DangerousPrototypes/BusPirate5-hardware/adapter-ir-toy-3REV3/datasheets/irm-36xxj7.png

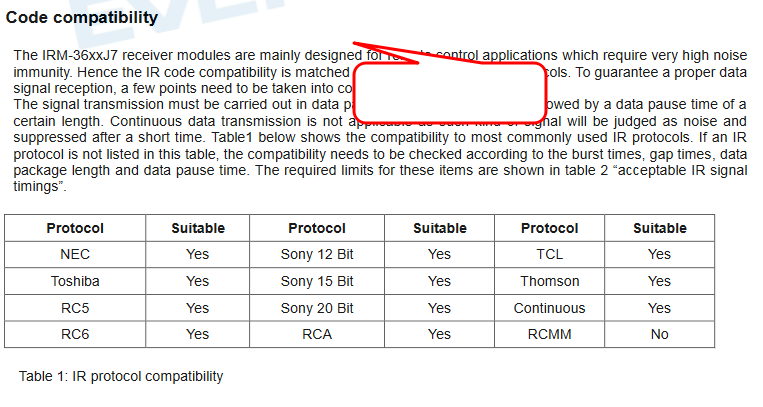
adapter-ir-toy-3REV3/datasheets/irm-36xxj7.png
