DangerousPrototypes/BusPirate5-hardware/bus_pirate_pcb/6-REV2B/6-REV2b.jpg

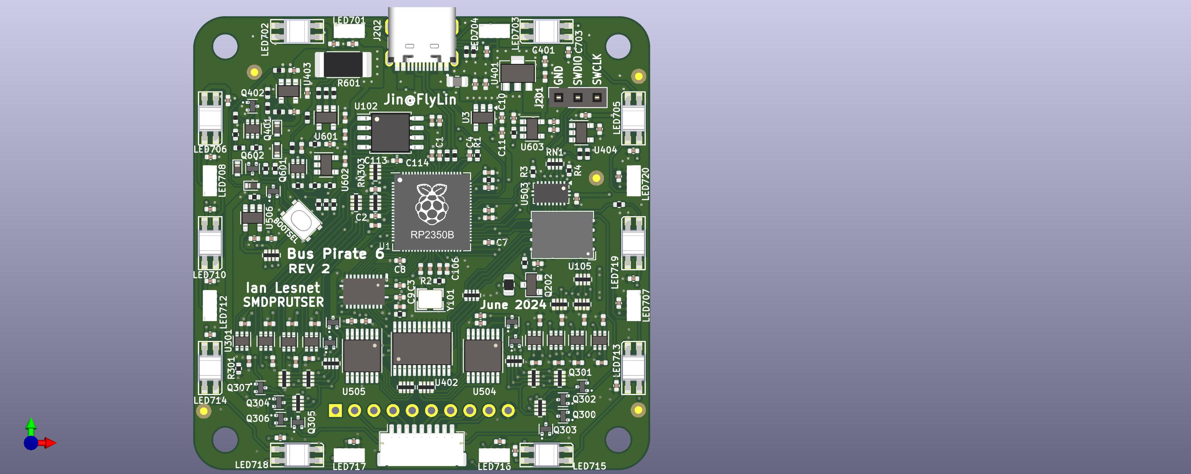
bus_pirate_pcb/6-REV2B/6-REV2b.jpg
