DangerousPrototypes/BusPirate5-hardware/bus_pirate_pcb/6-REV2B/6r2-pcb-top.png

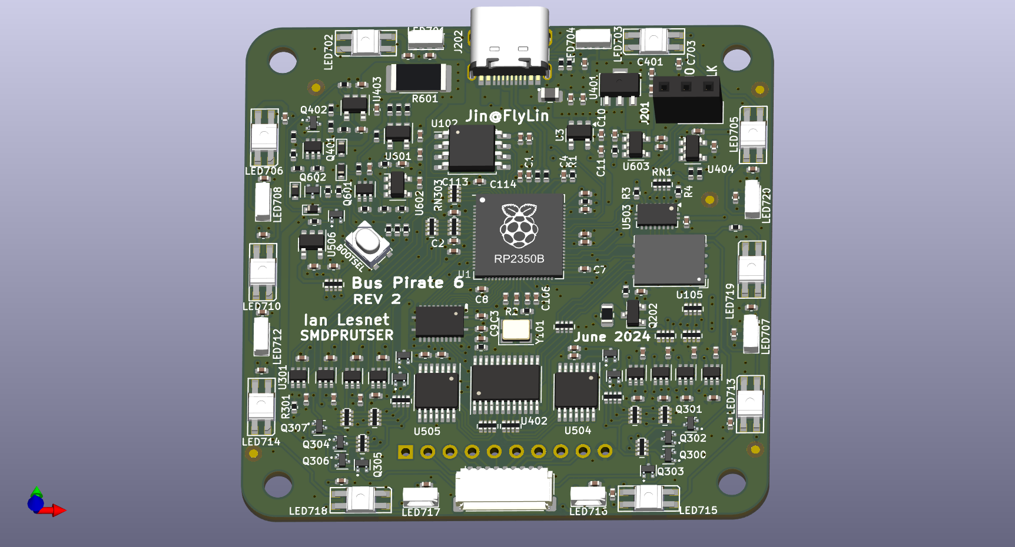
bus_pirate_pcb/6-REV2B/6r2-pcb-top.png
