DangerousPrototypes/BusPirate5-hardware/development/adapter-ram-ddr5-1REV0/ram-ddr5.jpg

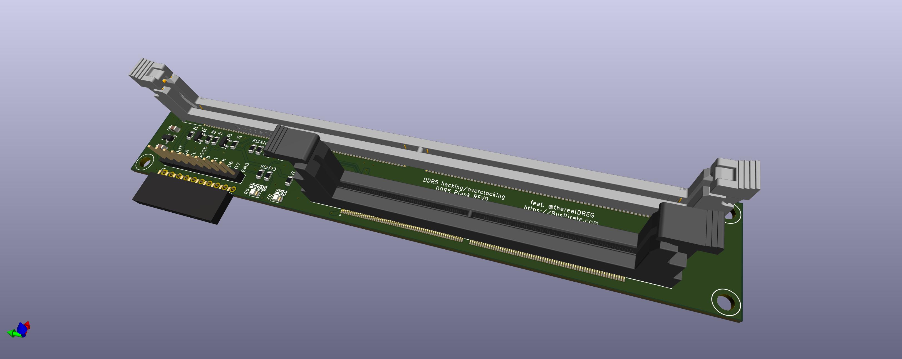
development/adapter-ram-ddr5-1REV0/ram-ddr5.jpg
