DangerousPrototypes/BusPirate5-hardware/development/adapter-ram-ddr5-1REV1/ram-ddr5-1REV1.jpg

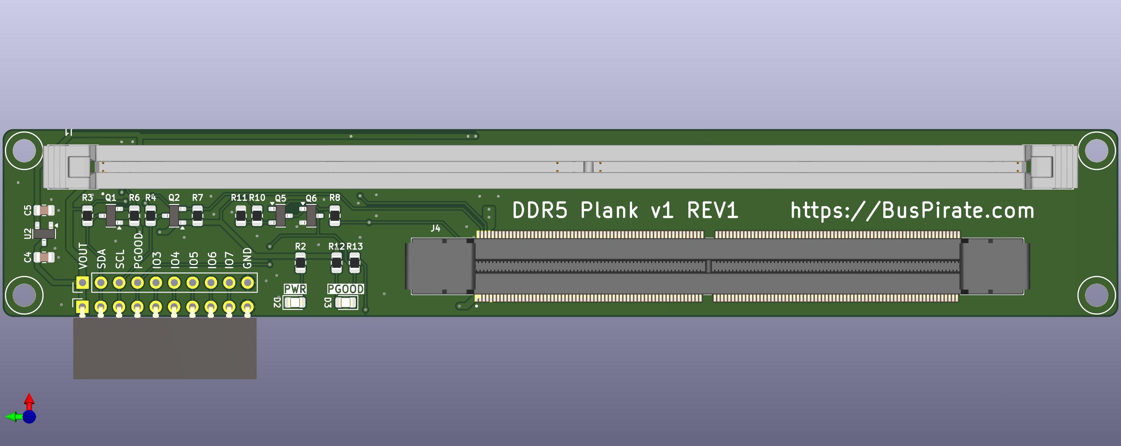
development/adapter-ram-ddr5-1REV1/ram-ddr5-1REV1.jpg
