DangerousPrototypes/BusPirate5-hardware/development/adapter-stemma-qwiic-grove-gravity-bog-1REV0/stemma-qwiic-grove-gravity-bog-plank.jpg

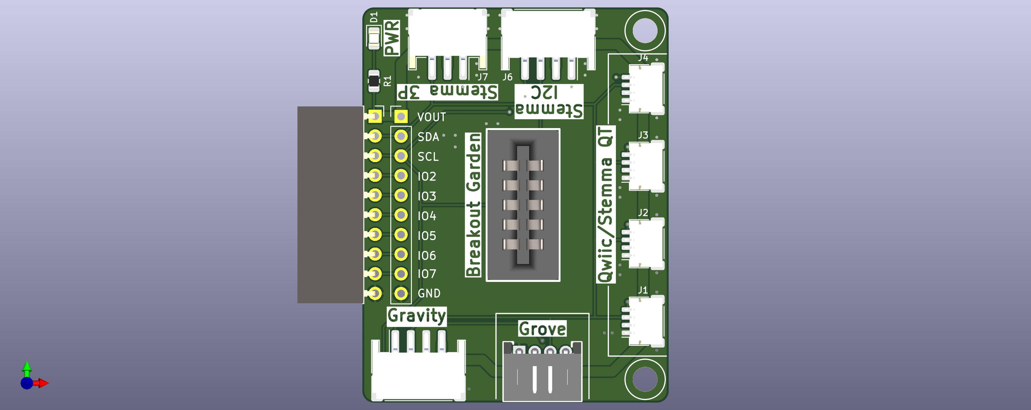
development/adapter-stemma-qwiic-grove-gravity-bog-1REV0/stemma-qwiic-grove-gravity-bog-plank.jpg
