DangerousPrototypes/BusPirate5-hardware/enclosure/BusPirate5REV8-v10-plug.png

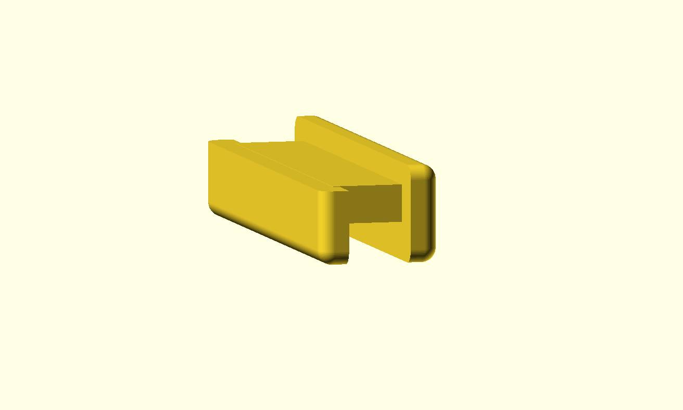
enclosure/BusPirate5REV8-v10-plug.png
