DangerousPrototypes/BusPirate5-hardware/enclosure/BusPirate5REV8-v10.png

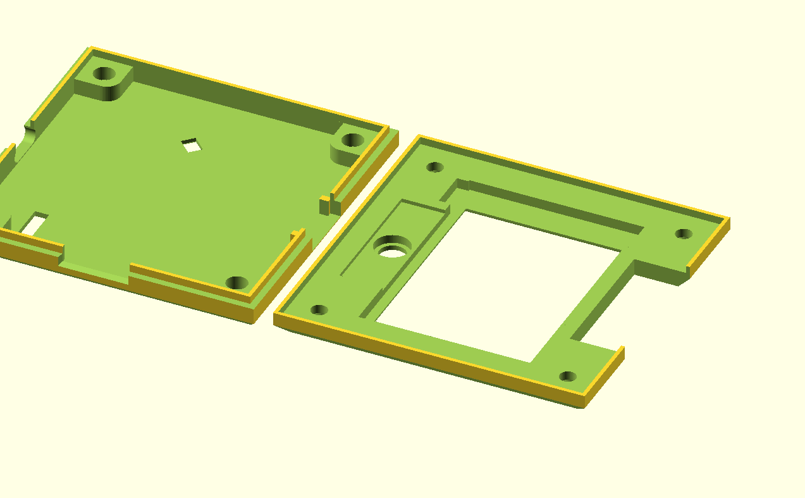
enclosure/BusPirate5REV8-v10.png
