DangerousPrototypes/BusPirate5-hardware/enclosure/enclosure-petg.jpg

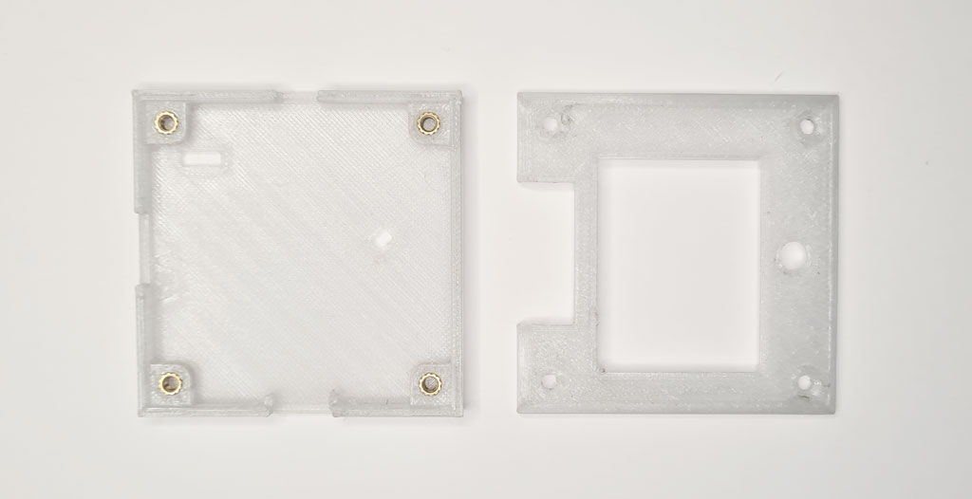
enclosure/enclosure-petg.jpg
