DangerousPrototypes/BusPirate5-hardware/milled-pins/pin-milled-rev1.jpg

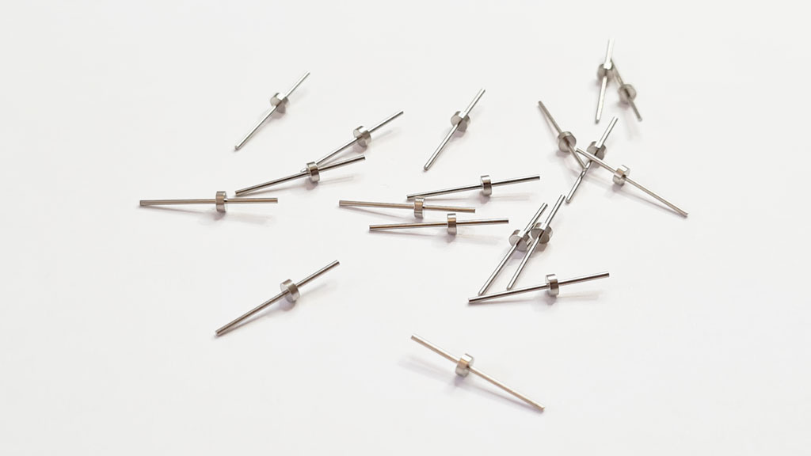
milled-pins/pin-milled-rev1.jpg
