DangerousPrototypes/BusPirate5-hardware/milled-pins/pin-milled-rev3.png

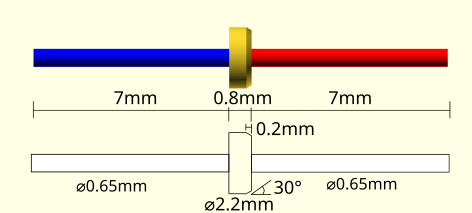
milled-pins/pin-milled-rev3.png
