DangerousPrototypes/BusPirate5-hardware/adapter-rs232-dual-1REV0/manuf/rs232-dual-adapter.xls

Source: | C:\buspirate5-hardware\rs232-dual-adapter\rs232-dual-adapter.kicad_sch
Date: | 2024-07-17T12:32:31+0200
Tool: | Eeschema 8.0.3
Generator: | C:\Program Files\KiCad\8.0\bin\scripting\plugins/bom_csv_grouped_by_value.py
Component Count: | 18
Collated Components:
Item | Qty | Reference(s) | Value | LibPart | Footprint | Datasheet | DNP | Datasheet | Description | Footprint
1 | 4 | C1, C2, C6, C7 | 0.1uF | Device:C_Small | Capacitor_SMD:C_0805_2012Metric | ~ |  | ~ | Unpolarized capacitor, small symbol | Capacitor_SMD:C_0805_2012Metric
2 | 6 | C3, C4, C5, C8, C9, C10 | 0.47uF | Device:C_Small | Capacitor_SMD:C_0805_2012Metric | ~ |  | ~ | Unpolarized capacitor, small symbol | Capacitor_SMD:C_0805_2012Metric
3 | 1 | D2 | LED | Device:LED | LED_SMD:LED_0805_2012Metric | ~ |  | ~ | Light emitting diode | LED_SMD:LED_0805_2012Metric
4 | 1 | J1 | COM1 | Connector:DE9_Plug_MountingHoles | Connector_Dsub:DSUB-9_Male_Horizontal_P2.77x2.84mm_EdgePinOffset7.70mm_Housed_MountingHolesOffset9.12mm | ~ |  | ~ | 9-pin male plug pin D-SUB connector, Mounting Hole | Connector_Dsub:DSUB-9_Male_Horizontal_P2.77x2.84mm_EdgePinOffset7.70mm_Housed_MountingHolesOffset9.12mm
5 | 1 | J2 | Conn_01x10 | Connector_Generic:Conn_01x10 | Connector_PinSocket_2.54mm:PinSocket_1x10_P2.54mm_Horizontal | ~ |  | ~ | Generic connector, single row, 01x10, script generated (kicad-library-utils/schlib/autogen/connector/) | Connector_PinSocket_2.54mm:PinSocket_1x10_P2.54mm_Horizontal
6 | 1 | J3 | Conn_01x10 | Connector_Generic:Conn_01x10 | Connector_PinHeader_2.54mm:PinHeader_1x10_P2.54mm_Vertical | ~ |  | ~ | Generic connector, single row, 01x10, script generated (kicad-library-utils/schlib/autogen/connector/) | Connector_PinHeader_2.54mm:PinHeader_1x10_P2.54mm_Vertical
7 | 1 | J4 | COM2 | Connector:DE9_Plug_MountingHoles | Connector_Dsub:DSUB-9_Female_Horizontal_P2.77x2.84mm_EdgePinOffset7.70mm_Housed_MountingHolesOffset9.12mm | ~ |  | ~ | 9-pin male plug pin D-SUB connector, Mounting Hole | Connector_Dsub:DSUB-9_Female_Horizontal_P2.77x2.84mm_EdgePinOffset7.70mm_Housed_MountingHolesOffset9.12mm
8 | 1 | R2 | 2K | Device:R | Resistor_SMD:R_0805_2012Metric | ~ |  | ~ | Resistor | Resistor_SMD:R_0805_2012Metric
9 | 2 | U1, U2 | MAX3232 | Interface_UART:MAX3232 | Package_SO:SOP-16_3.9x9.9mm_P1.27mm | https://datasheets.maximintegrated.com/en/ds/MAX3222-MAX3241.pdf |  | https://datasheets.maximintegrated.com/en/ds/MAX3222-MAX3241.pdf | 3.0V to 5.5V, Low-Power, up to 1Mbps, True RS-232 Transceivers Using Four 0.1μF External Capacitors | Package_SO:SOP-16_3.9x9.9mm_P1.27mm
 |  |  |  | Note: 80 with HGSemi, 20 with MAX3232
