DangerousPrototypes/BusPirate5-hardware/enclosure/BusPirate5REV10-v0.stl

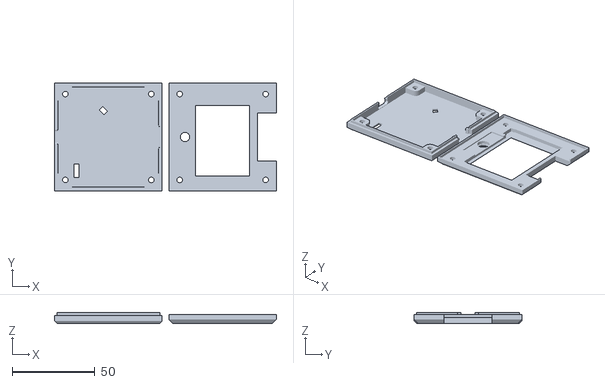
[picture p30: CAD file, 2024-01-15]
enclosure/BusPirate5REV10-v0.stl
134.4 x 65.2 x 6.40
