DangerousPrototypes/BusPirate5-hardware/development/adapter-stemma-qwiic-grove-gravity-bog-1REV0/footprints/SM04B-SRSS-TB (LF)(SN)--3DModel-STEP-269445.STEP

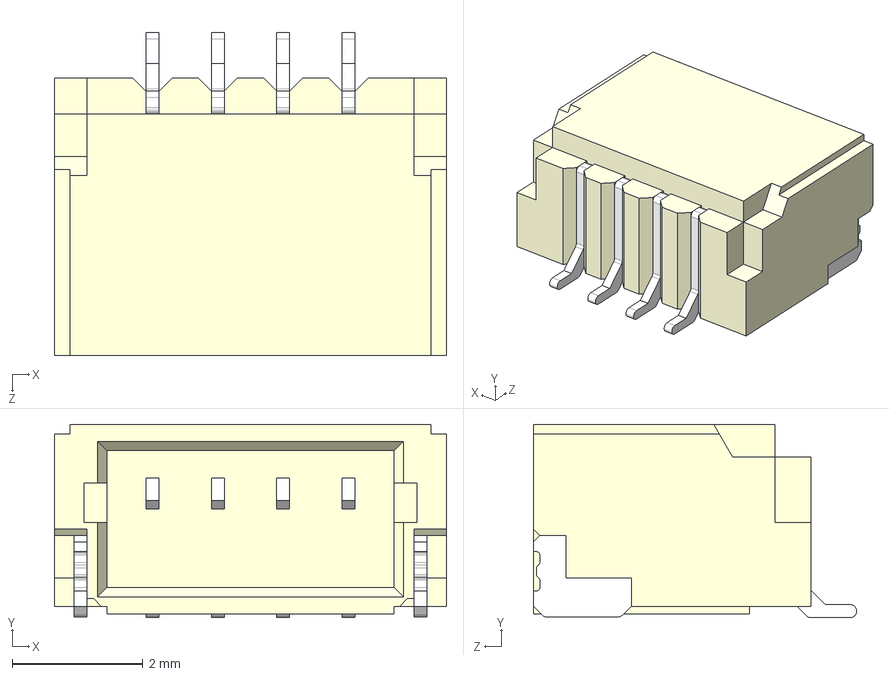
[picture p31: CAD file, 2025-06-16]
development/adapter-stemma-qwiic-grove-gravity-bog-1REV0/footprints/SM04B-SRSS-TB (LF)(SN)--3DModel-STEP-269445.STEP
6.00 x 2.96 x 4.95 mm
