DangerousPrototypes/BusPirate5-hardware/enclosure/BusPirate5REV8-v10-plug-rev2.stl

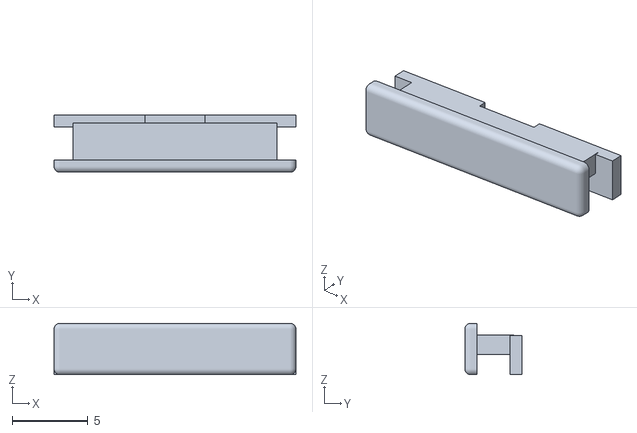
[picture p32: CAD file, 2024-01-15]
enclosure/BusPirate5REV8-v10-plug-rev2.stl
16.0 x 3.80 x 3.40
