DangerousPrototypes/BusPirate5-hardware/development/adapter-kaybee-plank-1REV0/footprints/HRO_TYPE-C-31-M-12.step

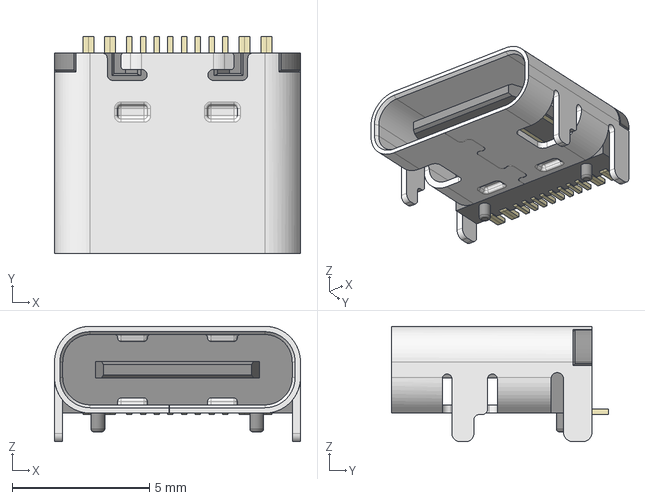
[picture p33: CAD file, 2025-02-23]
development/adapter-kaybee-plank-1REV0/footprints/HRO_TYPE-C-31-M-12.step
8.95 x 7.90 x 4.20 mm
