DangerousPrototypes/BusPirate5-hardware/development/adapter-stemma-qwiic-grove-gravity-bog-1REV0/footprints/3D_PCB1_2025-05-14.STEP

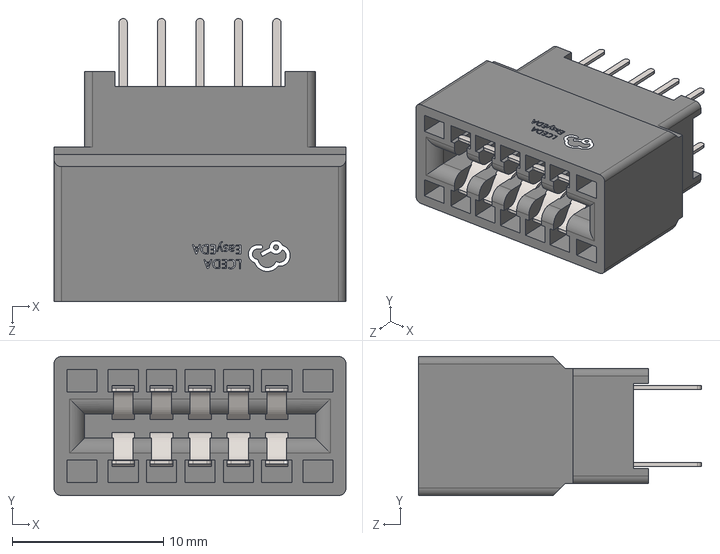
[picture p34: CAD file, 2025-06-16]
development/adapter-stemma-qwiic-grove-gravity-bog-1REV0/footprints/3D_PCB1_2025-05-14.STEP
19.3 x 9.20 x 18.7 mm
