DangerousPrototypes/BusPirate5-hardware/debug-station/debug-station-v3.png

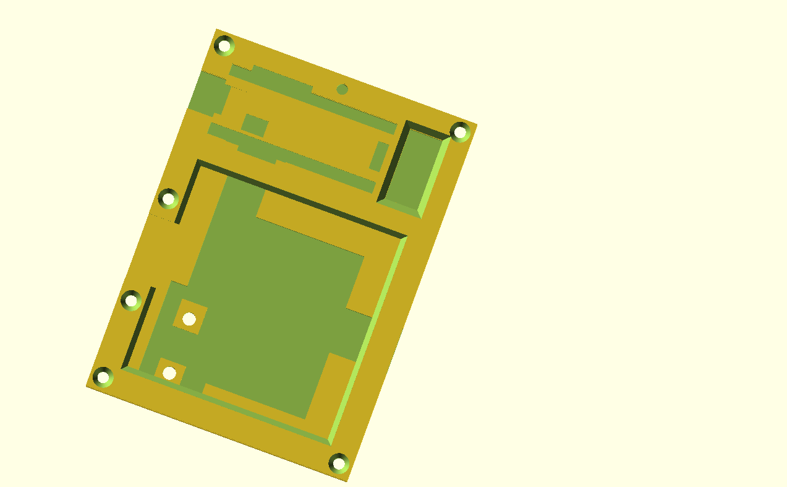
debug-station/debug-station-v3.png
