DangerousPrototypes/BusPirate5-hardware/bus_pirate_pcb/development/7-REV0A-prototype-1/plots/7-REV0__Assembly.pdf

1 | 2 | 3 | 4 | 5 | 6

A

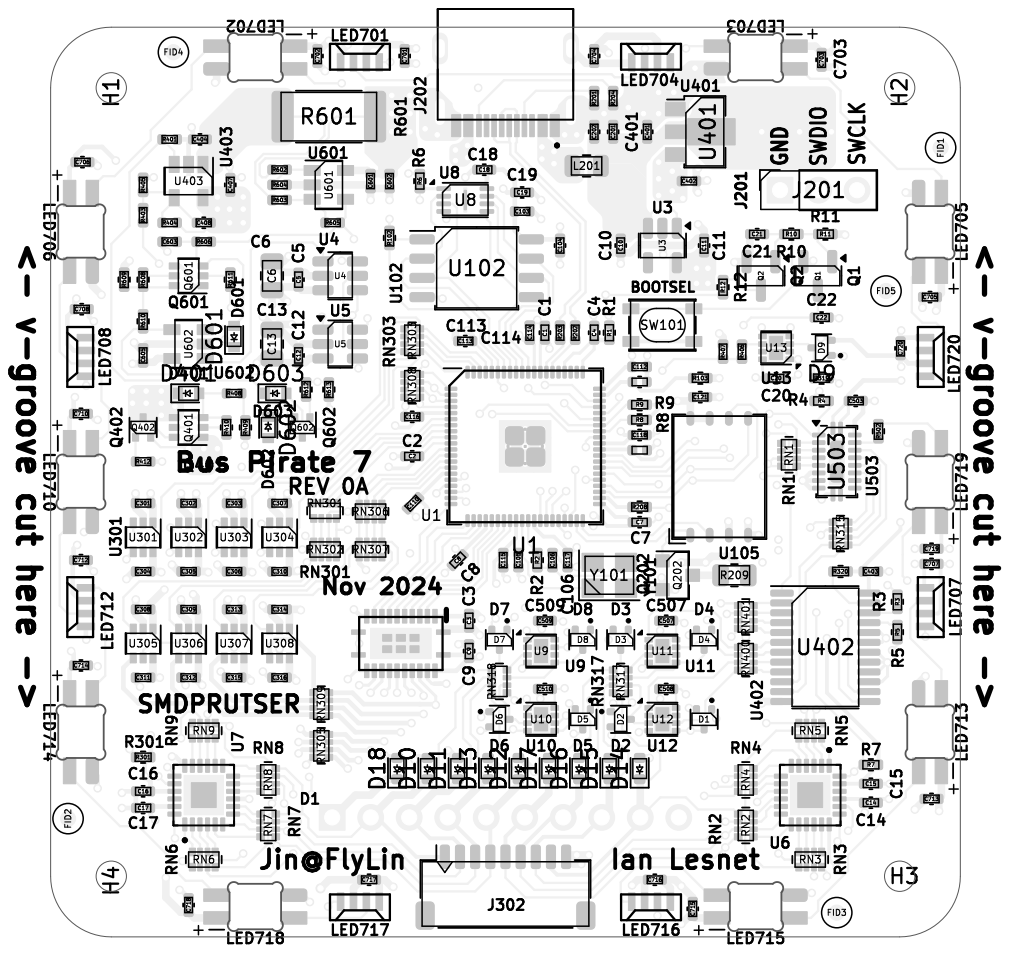
[picture p57: page 1]

Id: 1/1 Title: File: 7-REV0.kicad_pcb Sheet: Black-And-White-TOP

1 | 2 | 3 | 4 | 5 | 6

A

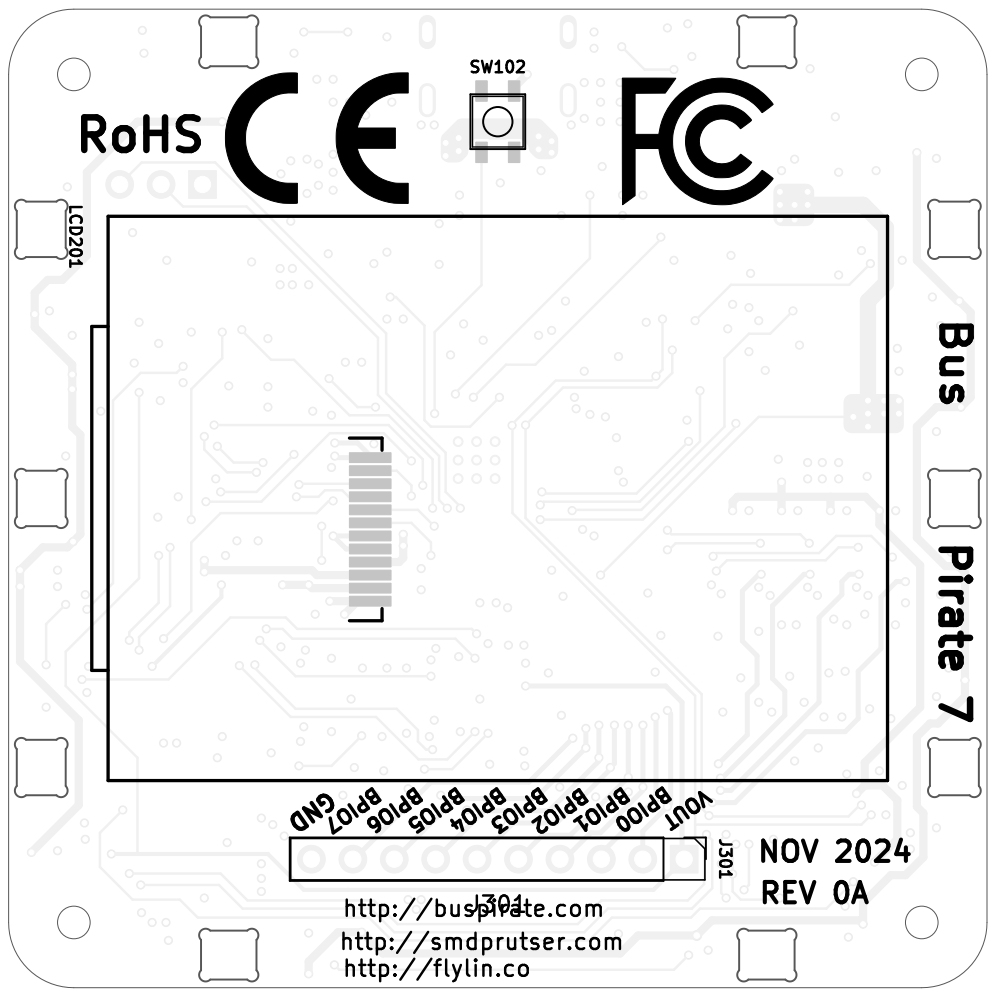
[picture p58: page 2]
http://smdprutser.com; J301 SW102 LCD201; D Date: KiCad; E.D.A. 8.0.7 Size: A4; Rev:; Id: 1/1 Title: File: 7-REV0.kicad_pcb Sheet: Black-And-White-BOT Board2Pdf:; Black-And-White-BOT; Page 2/2

http://flylin.co RoHS

http://buspirate.com
