DangerousPrototypes/BusPirate5-hardware/bus_pirate_pcb/development/7-REV2-prototype3a/plots/7-REV1B__Assembly.pdf

1 | 2 | 3 | 4 | 5 | 6

A

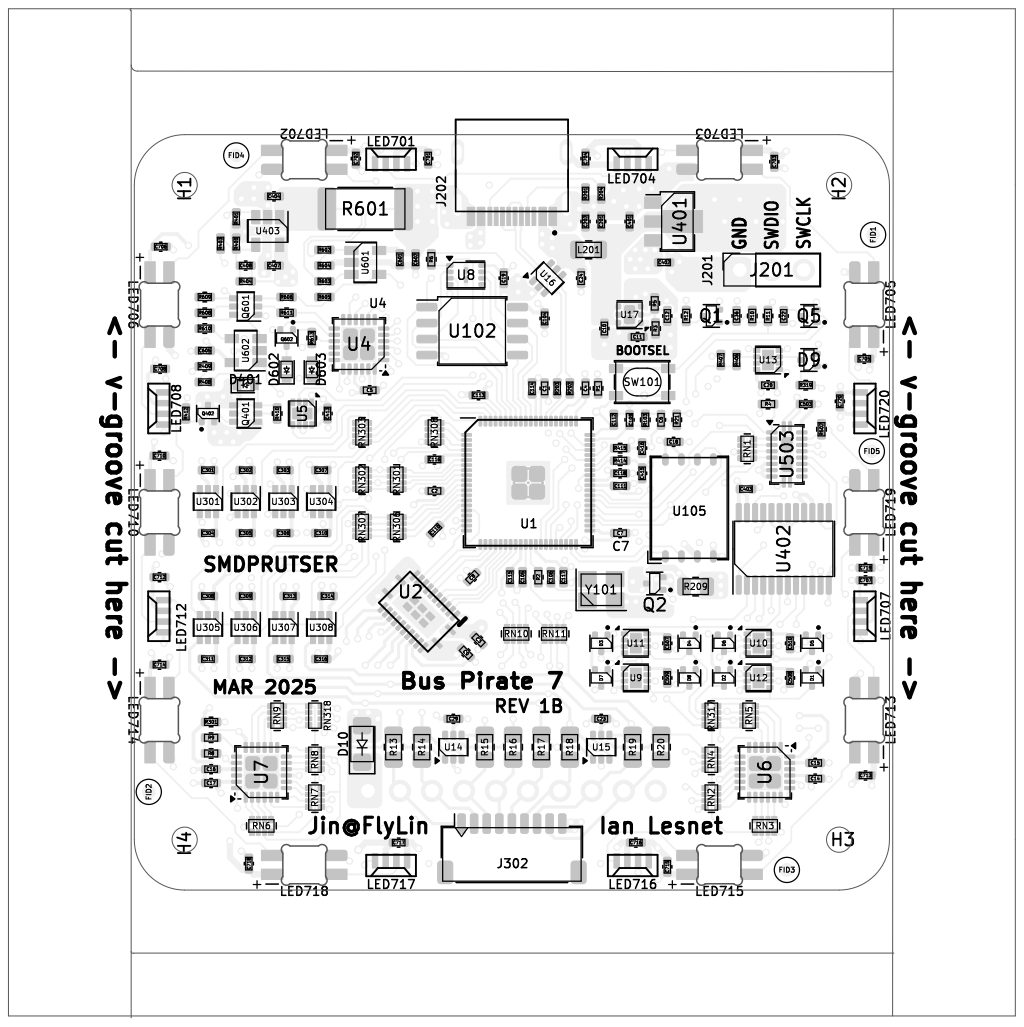
[picture p59: page 1]

GND SWDIO MAR 2025 SMDPRUTSER

Id: 1/1 Title: File: 7-REV1B.kicad_pcb Sheet: Black-And-White-TOP

1 | 2 | 3 | 4 | 5 | 6

A

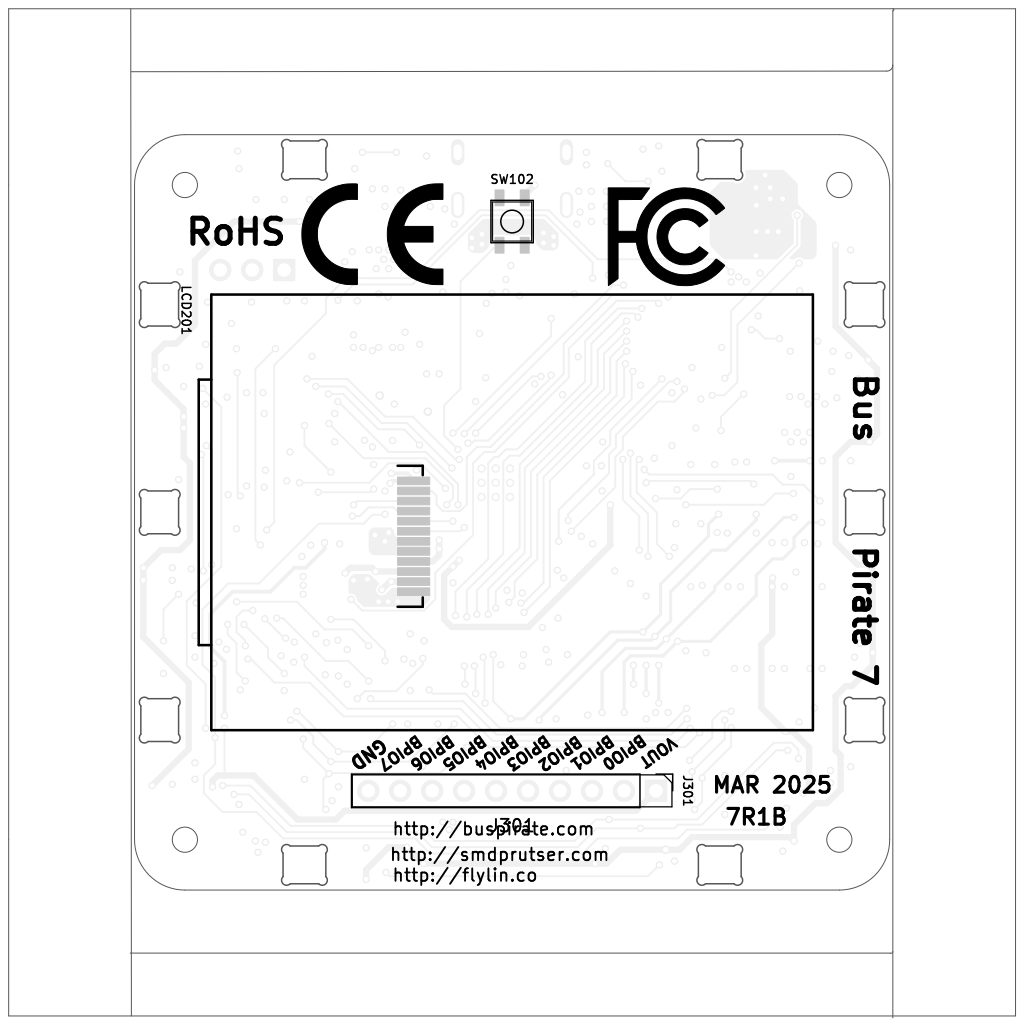
[picture p60: page 2]
http://smdprutser.com; J301 SW102 LCD201; D Date: KiCad; E.D.A. 8.0.7 Size: A4; Rev:; Id: 1/1 Title: File: 7-REV1B.kicad_pcb Sheet: Black-And-White-BOT Board2Pdf:; Black-And-White-BOT; Page 2/2

http://flylin.co RoHS

http://buspirate.com
