DangerousPrototypes/BusPirate5-hardware/development/adapter-flash-dip-1REV4/flash-dip-rev4.kicad_pcb

## KiCad design development/adapter-flash-dip-1REV4/flash-dip-rev4.kicad_pcb (2025-06-16)

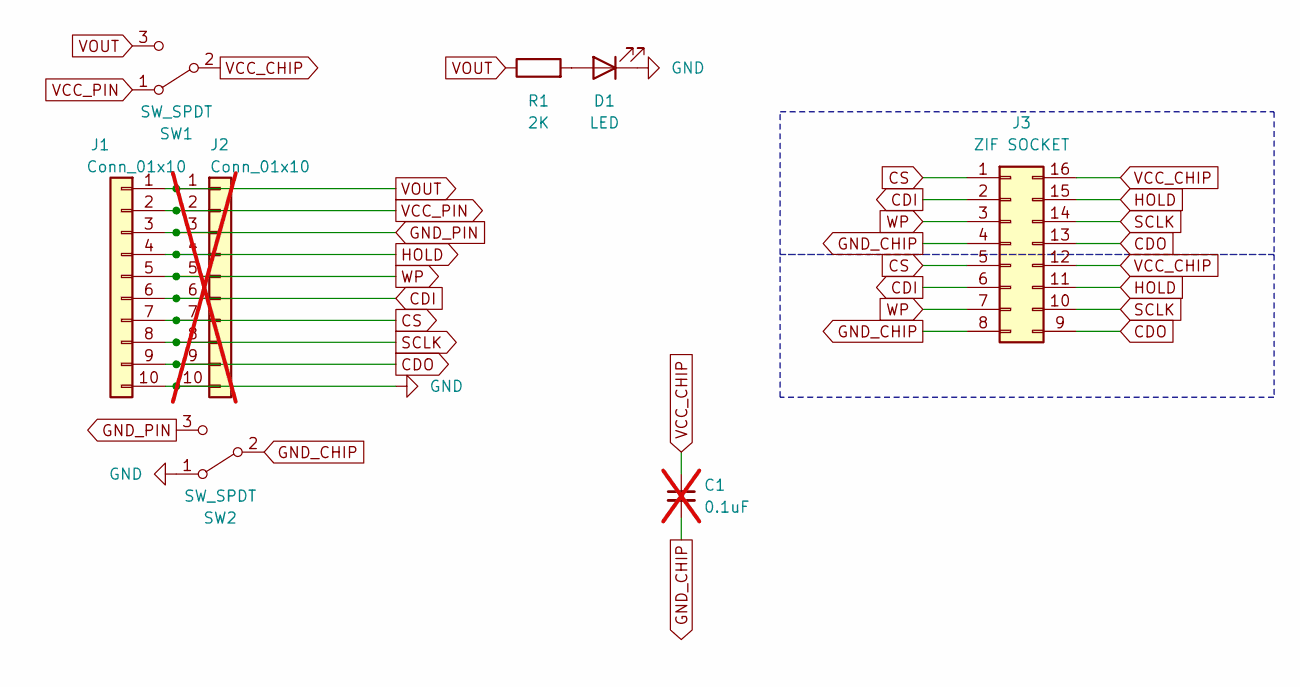
[picture p82: schematic flash-dip-rev4.kicad_sch]

Parts:
C1: 0.1uF; C_0805_2012Metric; not fitted
D1: LED; LED_0805_2012Metric
J1: Conn_01x10; PinSocket_1x10_P2.54mm_Horizontal
J2: Conn_01x10; PinHeader_1x10_P2.54mm_Vertical; not fitted
J3: ZIF SOCKET; DIP_Socket-16_W4.3_W5.08_W7.62_W10.16_W10.9_3M_216-3340-00-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
R1: 2K; R_0805_2012Metric
SW1, SW2: SW_SPDT; SW_SPDT_PCM12

Connections:
CDI: J1.6, J2.6, J3.2, J3.6
CDO: J1.9, J2.9, J3.9, J3.13
CS: J1.7, J2.7, J3.1, J3.5
GND: D1.1 (K), J1.10, J2.10, SW2.1 (A)
GND_CHIP: C1.2, J3.4, J3.8, SW2.2 (B)
GND_PIN: J1.3, J2.3, SW2.3 (C)
HOLD: J1.4, J2.4, J3.11, J3.15
unnamed: D1.2 (A), R1.2
SCLK: J1.8, J2.8, J3.10, J3.14
VCC_CHIP: C1.1, J3.12, J3.16, SW1.2 (B)
VCC_PIN: J1.2, J2.2, SW1.1 (A)
VOUT: J1.1, J2.1, R1.1, SW1.3 (C)
WP: J1.5, J2.5, J3.3, J3.7

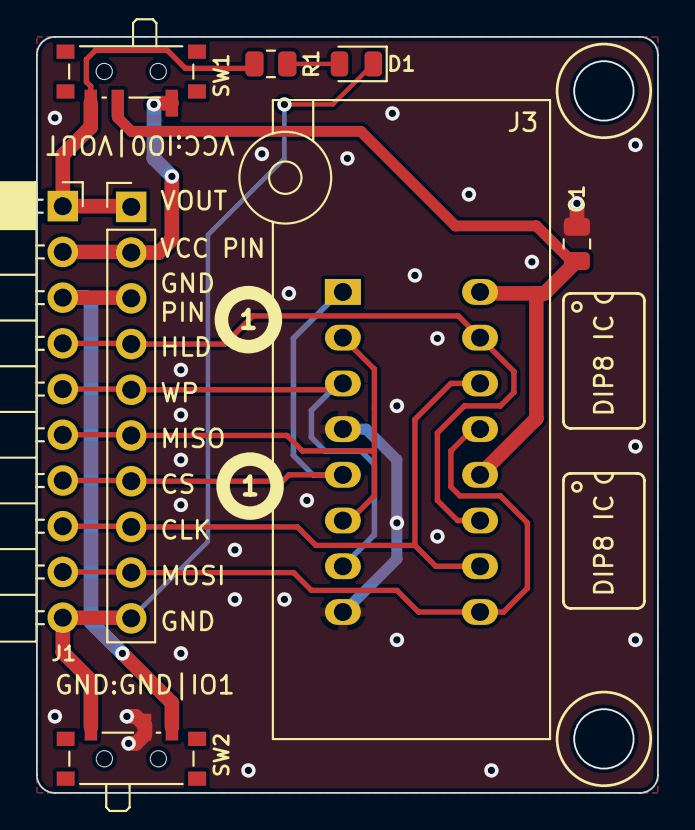
[picture p83: board flash-dip-rev4.kicad_pcb from above]

Board: 2 copper layers, 34.5 x 42.0 mm, 8 parts (0 on the bottom side), 13 nets.
