DangerousPrototypes/BusPirate5-hardware/development/adapter-sim-iccard-1REV4/sim-iccard-rev4.kicad_pcb

## KiCad design development/adapter-sim-iccard-1REV4/sim-iccard-rev4.kicad_pcb (2025-06-16)

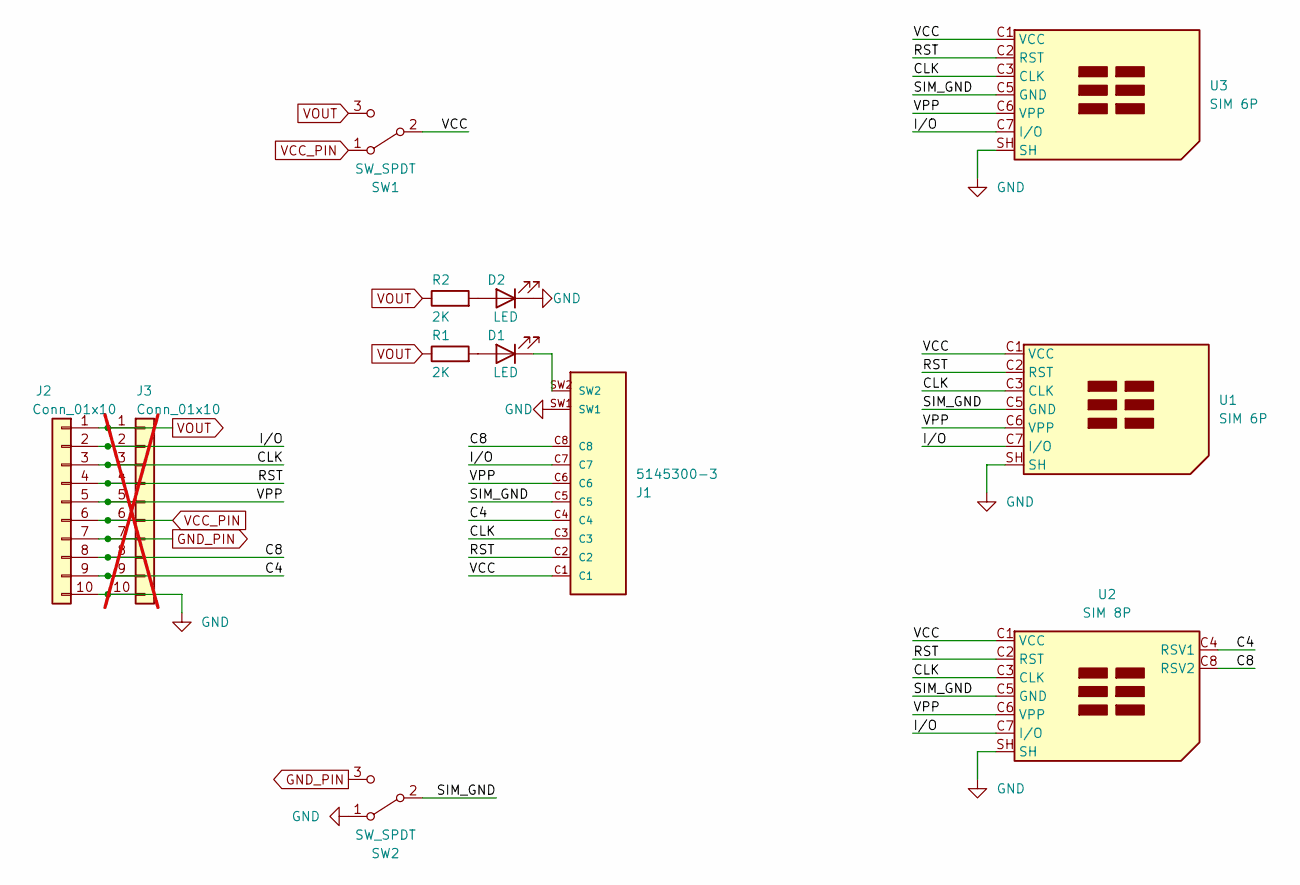
[picture p84: schematic sim-iccard-rev4.kicad_sch]

Parts:
D1, D2: LED; LED_0805_2012Metric
J1: 5145300-3; TE_5145300-3; PARTREV C3
J2: Conn_01x10; PinSocket_1x10_P2.54mm_Horizontal
J3: Conn_01x10; PinHeader_1x10_P2.54mm_Vertical; not fitted
R1, R2: 2K; R_0805_2012Metric
SW1, SW2: SW_SPDT; SW_SPDT_PCM12
U1: SIM 6P; DGLZ-SIM-0004
U2: SIM 8P; SIM-0030
U3: SIM 6P; SIM-0036

Connections:
/C4: J1.C4, J2.9, J3.9, U2.C4 (RSV1)
/C8: J1.C8, J2.8, J3.8, U2.C8 (RSV2)
/CLK: J1.C3, J2.3, J3.3, U1.C3 (CLK), U2.C3 (CLK), U3.C3 (CLK)
/I/O: J1.C7, J2.2, J3.2, U1.C7 (I/O), U2.C7 (I/O), U3.C7 (I/O)
/RST: J1.C2, J2.4, J3.4, U1.C2 (RST), U2.C2 (RST), U3.C2 (RST)
/SIM_GND: J1.C5, SW2.2 (B), U1.C5 (GND), U2.C5 (GND), U3.C5 (GND)
/VCC: J1.C1, SW1.2 (B), U1.C1 (VCC), U2.C1 (VCC), U3.C1 (VCC)
/VPP: J1.C6, J2.5, J3.5, U1.C6 (VPP), U2.C6 (VPP), U3.C6 (VPP)
GND: D2.1 (K), J1.SW1, J2.10, J3.10, SW2.1 (A), U1.SH, U2.SH, U3.SH
GND_PIN: J2.7, J3.7, SW2.3 (C)
unnamed: D1.2 (A), R1.2
unnamed: D1.1 (K), J1.SW2
unnamed: D2.2 (A), R2.2
VCC_PIN: J2.6, J3.6, SW1.1 (A)
VOUT: J2.1, J3.1, R1.1, R2.1, SW1.3 (C)

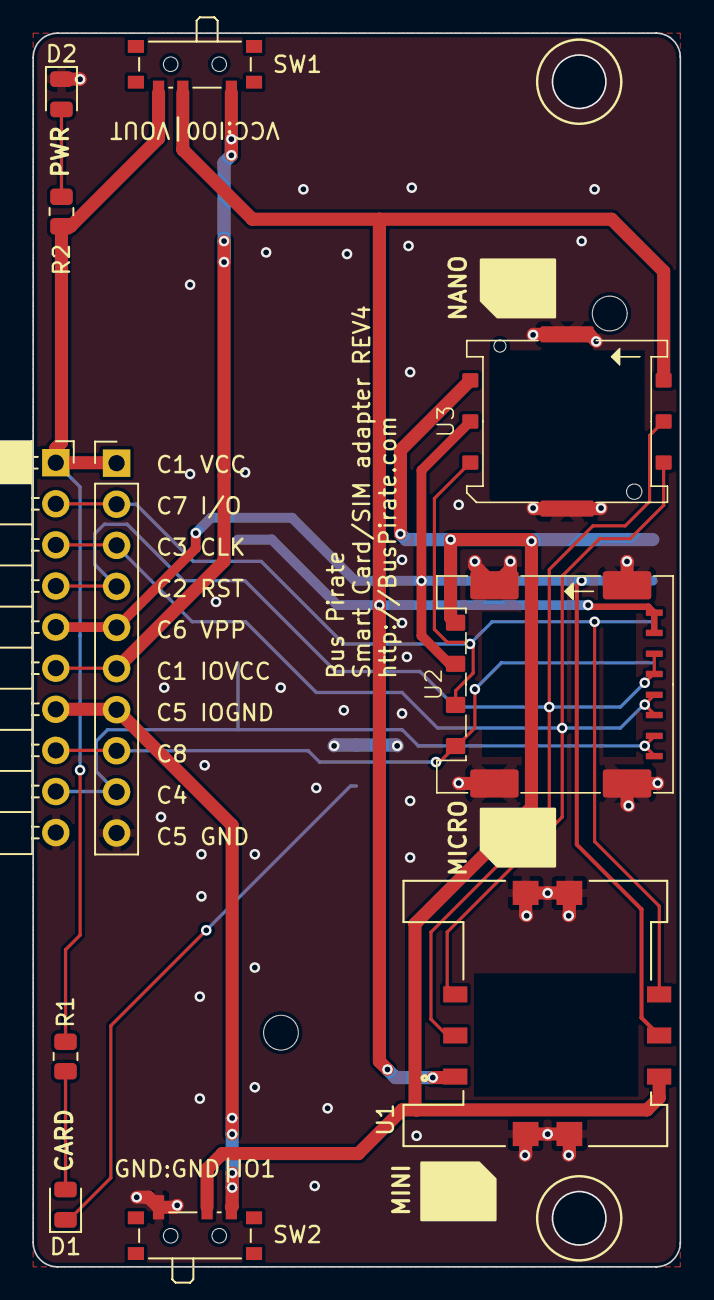
[picture p85: board sim-iccard-rev4.kicad_pcb from above]

Board: 2 copper layers, 40.0 x 76.2 mm, 12 parts (1 on the bottom side), 15 nets.
