DangerousPrototypes/BusPirate5-hardware/adapter-flash-wson-1REV3/flash-wson-rev3.kicad_pcb

## KiCad design adapter-flash-wson-1REV3/flash-wson-rev3.kicad_pcb (2025-06-16)

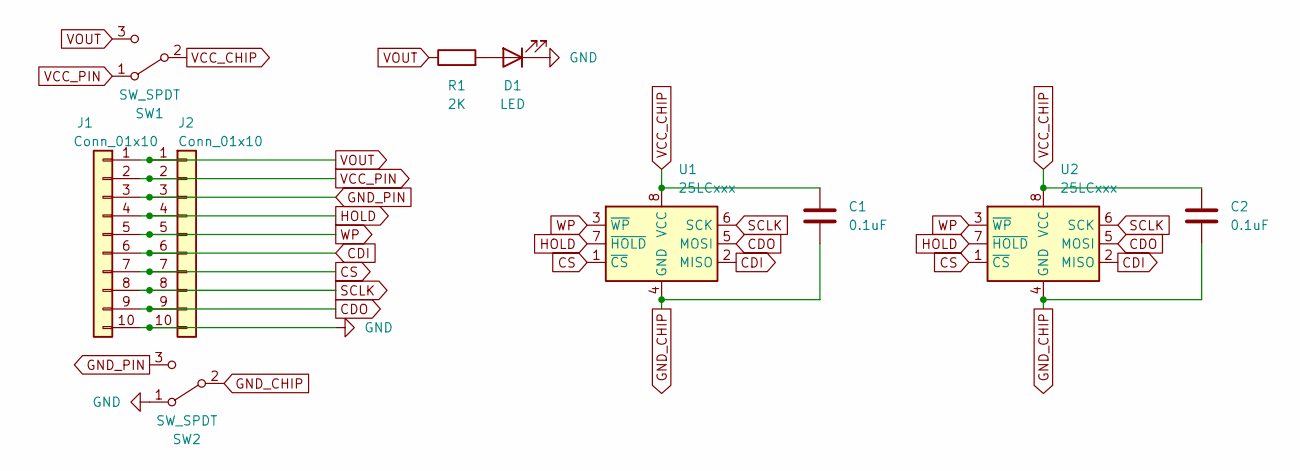
[picture p86: schematic flash-wson-rev3.kicad_sch]

Parts:
C1, C2: 0.1uF; C_0805_2012Metric
D1: LED; LED_0805_2012Metric
J1: Conn_01x10; PinSocket_1x10_P2.54mm_Horizontal
J2: Conn_01x10; PinHeader_1x10_P2.54mm_Vertical
R1: 2K; R_0805_2012Metric
SW1, SW2: SW_SPDT; SW_SPDT_PCM12
U1: 25LCxxx; WSON-5x6
U2: 25LCxxx; WSON8-6x8

Connections:
CDI: J1.6, J2.6, U1.2 (MISO), U2.2 (MISO)
CDO: J1.9, J2.9, U1.5 (MOSI), U2.5 (MOSI)
CS: J1.7, J2.7, U1.1 (~CS), U2.1 (~CS)
GND: D1.1 (K), J1.10, J2.10, SW2.1 (A)
GND_CHIP: C1.2, C2.2, SW2.2 (B), U1.4 (GND), U2.4 (GND)
GND_PIN: J1.3, J2.3, SW2.3 (C)
HOLD: J1.4, J2.4, U1.7 (~HOLD), U2.7 (~HOLD)
unnamed: D1.2 (A), R1.2
SCLK: J1.8, J2.8, U1.6 (SCK), U2.6 (SCK)
VCC_CHIP: C1.1, C2.1, SW1.2 (B), U1.8 (VCC), U2.8 (VCC)
VCC_PIN: J1.2, J2.2, SW1.1 (A)
VOUT: J1.1, J2.1, R1.1, SW1.3 (C)
WP: J1.5, J2.5, U1.3 (~WP), U2.3 (~WP)

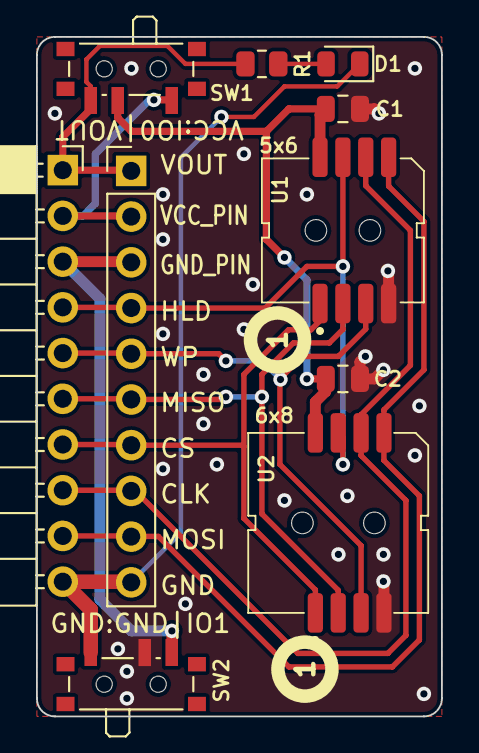
[picture p87: board flash-wson-rev3.kicad_pcb from above]

Board: 2 copper layers, 22.5 x 37.8 mm, 10 parts (0 on the bottom side), 13 nets.
