DangerousPrototypes/BusPirate5-hardware/adapter-ir-toy-3REV3/bp5-ir-toy-v3-rev3.kicad_pcb

## KiCad design adapter-ir-toy-3REV3/bp5-ir-toy-v3-rev3.kicad_pcb (2025-06-16)

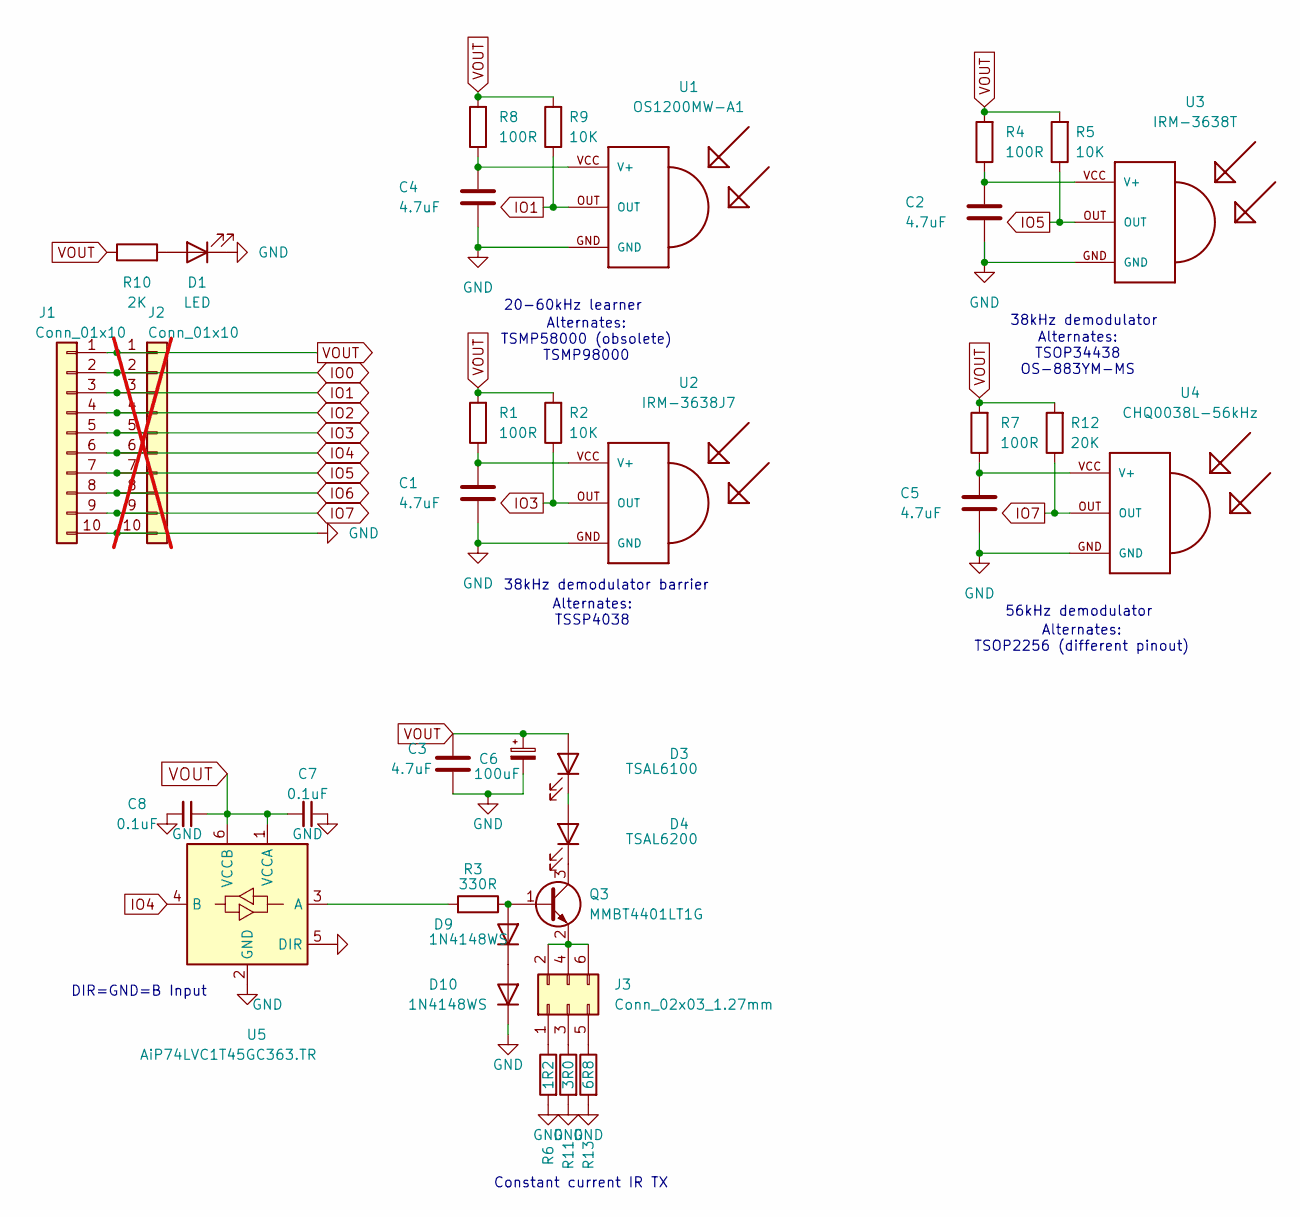
[picture p88: schematic bp5-ir-toy-v3-rev3.kicad_sch]

Parts:
C1, C2, C3, C4, C5: 4.7uF; C_0805_2012Metric
C6: 100uF; CP_EIA-3528-21_Kemet-B_Pad1.50x2.35mm_HandSolder
C7, C8: 0.1uF; C_0805_2012Metric
D1: LED; LED_0805_2012Metric
D3: TSAL6100; LED_D5.0mm_Horizontal_O1.27mm_Z3.0mm_IRGrey
D4: TSAL6200; LED_D5.0mm_Horizontal_O1.27mm_Z3.0mm_IRGrey
D9, D10: 1N4148WS; D_SOD-323F
J1: Conn_01x10; PinSocket_1x10_P2.54mm_Horizontal
J2: Conn_01x10; PinHeader_1x10_P2.54mm_Vertical; not fitted
J3: Conn_02x03_1.27mm; PinHeader_2x03_P1.27mm_Vertical
Q3: MMBT4401LT1G; SOT-23
R1, R4, R7, R8: 100R; R_0805_2012Metric
R2, R5, R9: 10K; R_0805_2012Metric
R3: 330R; R_0805_2012Metric
R6: 1R2; R_1206_3216Metric
R10: 2K; R_0805_2012Metric
R11: 3R0; R_1206_3216Metric
R12: 20K; R_0805_2012Metric
R13: 6R8; R_1206_3216Metric
U1: OS1200MW-A1; TSOP18XX
U2: IRM-3638J7; TSOP18XX
U3: IRM-3638T; TSOP18XX
U4: CHQ0038L-56kHz; TSOP18XX
U5: AiP74LVC1T45GC363.TR; SOT-363_SC-70-6

Connections:
GND: C1.2, C2.2, C3.2, C4.2, C5.2, C6.2, C7.1, C8.2, D1.1 (K), D10.1 (K), J1.10, J2.10, R6.2, R11.2, R13.2, U1.GND, U2.GND, U3.GND, U4.GND, U5.2 (GND), U5.5 (DIR)
IO0: J1.2, J2.2
IO1: J1.3, J2.3, R9.1, U1.OUT
IO2: J1.4, J2.4
IO3: J1.5, J2.5, R2.1, U2.OUT
IO4: J1.6, J2.6, U5.4 (B)
IO5: J1.7, J2.7, R5.1, U3.OUT
IO6: J1.8, J2.8
IO7: J1.9, J2.9, R12.1, U4.OUT
unnamed: D1.2 (A), R10.2
unnamed: D3.1 (K), D4.2 (A)
unnamed: D4.1 (K), Q3.3 (C)
unnamed: D9.2 (A), Q3.1 (B), R3.1
unnamed: D9.1 (K), D10.2 (A)
unnamed: J3.1, R6.1
unnamed: J3.2, J3.4, J3.6, Q3.2 (E)
unnamed: J3.3, R11.1
unnamed: J3.5, R13.1
unnamed: C4.1, R8.1, U1.VCC (V+)
unnamed: C1.1, R1.1, U2.VCC (V+)
unnamed: C2.1, R4.1, U3.VCC (V+)
unnamed: C5.1, R7.1, U4.VCC (V+)
unnamed: R3.2, U5.3 (A)
VOUT: C3.1, C6.1, C7.2, C8.1, D3.2 (A), J1.1, J2.1, R1.2, R2.2, R4.2, R5.2, R7.2, R8.2, R9.2, R10.1, R12.2, U5.1 (VCCA), U5.6 (VCCB)

Notes on the sheet:
Constant current IR TX
38kHz demodulator
56kHz demodulator
Alternates: TSMP58000 (obsolete) TSMP98000
38kHz demodulator barrier
Alternates: TSOP2256 (different pinout)
Alternates: TSOP34438 OS-883YM-MS
Alternates: TSSP4038
20-60kHz learner
DIR=GND=B Input

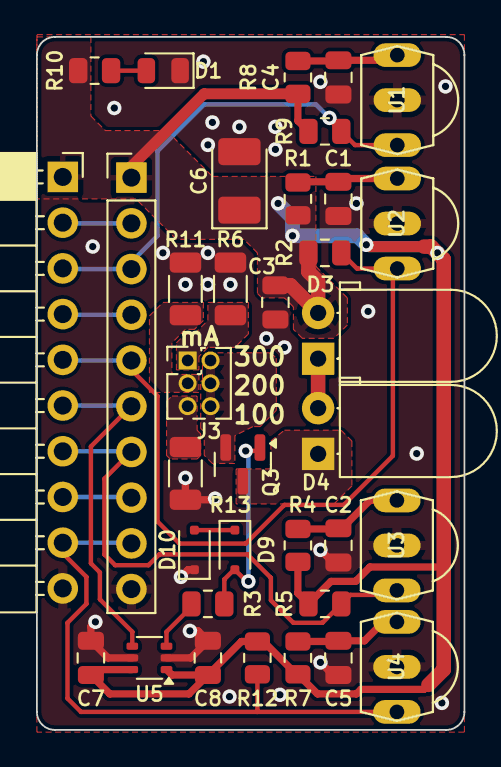
[picture p89: board bp5-ir-toy-v3-rev3.kicad_pcb from above]

Board: 2 copper layers, 23.8 x 38.5 mm, 35 parts (0 on the bottom side), 24 nets.
