DangerousPrototypes/BusPirate5-hardware/adapter-blank-plank-1REV0B/blank-plank-rev0b.kicad_pcb

## KiCad design adapter-blank-plank-1REV0B/blank-plank-rev0b.kicad_pcb (2025-06-16)

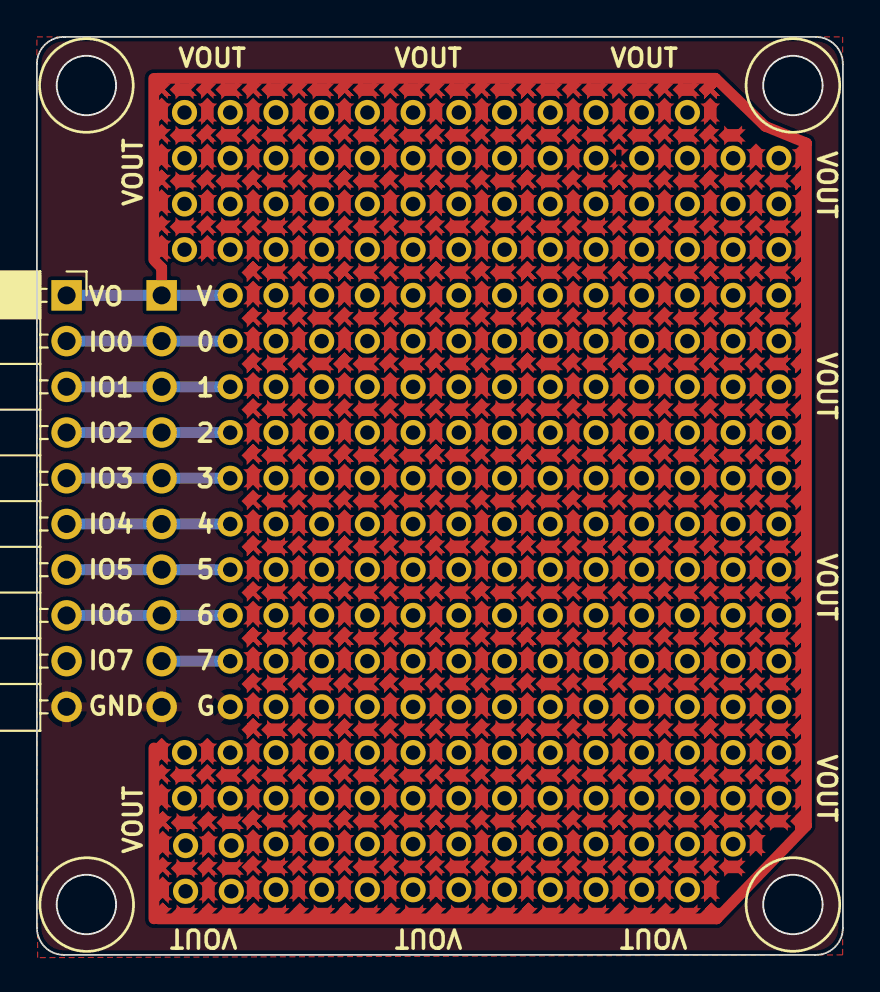
[picture p90: board blank-plank-rev0b.kicad_pcb from above]

Board: 2 copper layers, 44.8 x 51.0 mm, 3 parts (0 on the bottom side), 10 nets.

Parts:
J2: Conn_01x10; PinSocket_1x10_P2.54mm_Horizontal
J3: Conn_01x10; PinHeader_1x10_P2.54mm_Vertical_No_Silk
J5: Conn_01x10; PinHeader_1x10_P2.54mm_Vertical_Reduced_2

Connections:
GND: J2.10, J3.10, J5.10
IO0: J2.2, J3.2, J5.2
IO1: J2.3, J3.3, J5.3
IO2: J2.4, J3.4, J5.4
IO3: J2.5, J3.5, J5.5
IO4: J2.6, J3.6, J5.6
IO5: J2.7, J3.7, J5.7
IO6: J2.8, J3.8, J5.8
IO7: J2.9, J3.9, J5.9
VOUT: J2.1, J3.1, J5.1
