DangerousPrototypes/BusPirate5-hardware/adapter-vpp-maker-1REV6/vpp-maker-rev6-ian.kicad_pcb

## KiCad design adapter-vpp-maker-1REV6/vpp-maker-rev6-ian.kicad_pcb (2025-06-16)

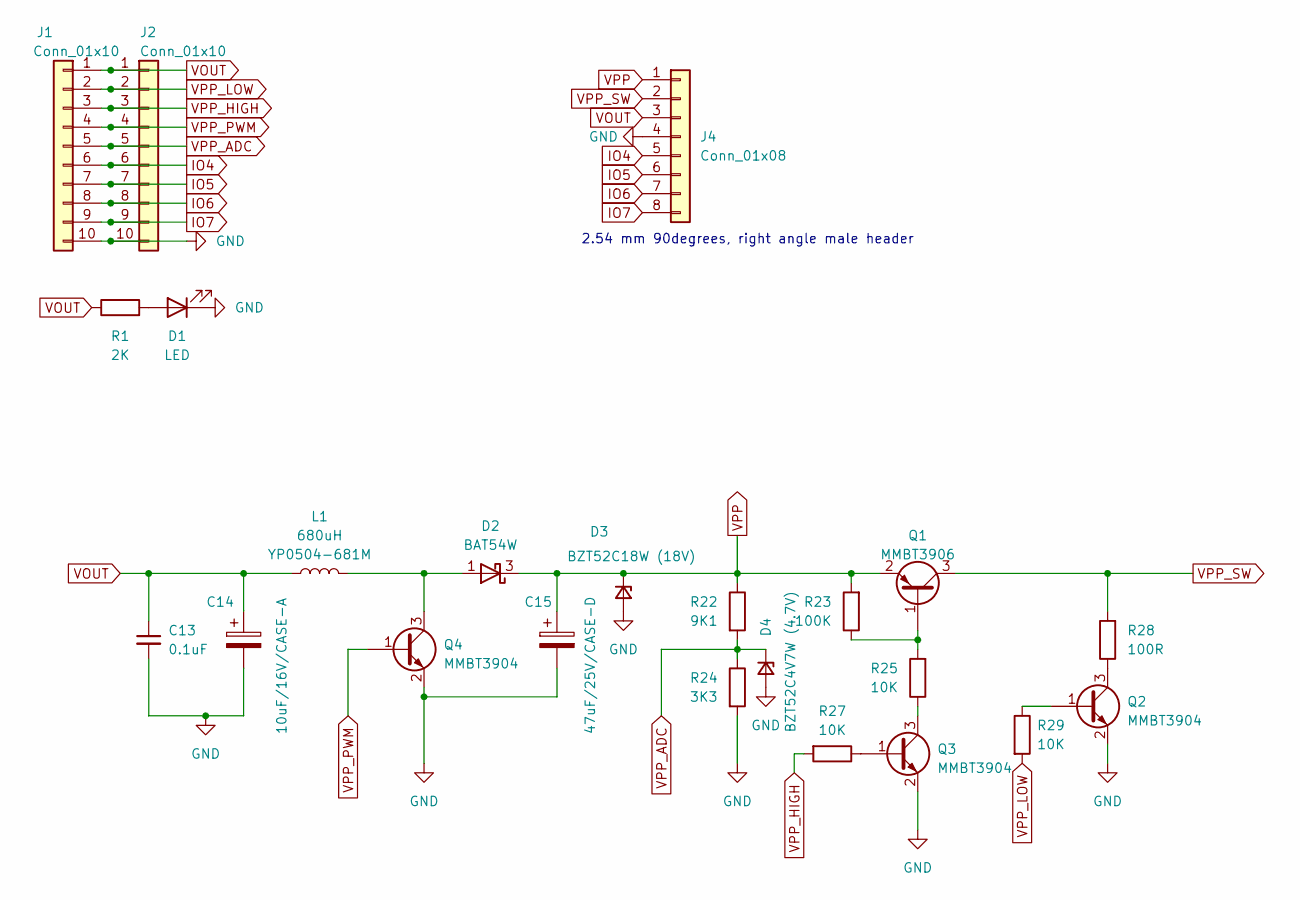
[picture p91: schematic vpp-maker-rev6-ian.kicad_sch]

Parts:
C13: 0.1uF; C_0805_2012Metric_Pad1.18x1.45mm_HandSolder
C14: 10uF/16V/CASE-A; CP_EIA-3216-18_Kemet-A
C15: 47uF/25V/CASE-D; CP_EIA-7343-31_Kemet-D
D1: LED; LED_0805_2012Metric
D2: BAT54W; SOT-23
D3: BZT52C18W (18V); D_SOD-123
D4: BZT52C4V7W (4.7V); D_SOD-123
J1: Conn_01x10; PinSocket_1x10_P2.54mm_Horizontal
J2: Conn_01x10; PinHeader_1x10_P2.54mm_Vertical
J4: Conn_01x08; PinHeader_1x08_P2.54mm_Horizontal
L1: 680uH; L_YP0504; MPN YP0504-681M
Q1: MMBT3906; SOT-23
Q2, Q3, Q4: MMBT3904; SOT-23
R1: 2K; R_0805_2012Metric
R22: 9K1; R_0805_2012Metric
R23: 100K; R_0805_2012Metric
R24: 3K3; R_0805_2012Metric
R25, R27, R29: 10K; R_0805_2012Metric
R28: 100R; R_0805_2012Metric

Connections:
GND: C13.2, C14.2, C15.2, D1.1 (K), D3.2 (A), D4.2 (A), J1.10, J2.10, J4.4, Q2.2 (E), Q3.2 (E), Q4.2 (E), R24.2
IO4: J1.6, J2.6, J4.5
IO5: J1.7, J2.7, J4.6
IO6: J1.8, J2.8, J4.7
IO7: J1.9, J2.9, J4.8
unnamed: D1.2 (A), R1.2
unnamed: D2.1 (A), L1.2, Q4.3 (C)
unnamed: Q1.1 (B), R23.1, R25.2
unnamed: Q2.1 (B), R29.1
unnamed: Q2.3 (C), R28.1
unnamed: Q3.1 (B), R27.1
unnamed: Q3.3 (C), R25.1
VOUT: C13.1, C14.1, J1.1, J2.1, J4.3, L1.1, R1.1
VPP: C15.1, D2.3 (K), D3.1 (K), J4.1, Q1.2 (E), R22.1, R23.2
VPP_ADC: D4.1 (K), J1.5, J2.5, R22.2, R24.1
VPP_HIGH: J1.3, J2.3, R27.2
VPP_LOW: J1.2, J2.2, R29.2
VPP_PWM: J1.4, J2.4, Q4.1 (B)
VPP_SW: J4.2, Q1.3 (C), R28.2

Notes on the sheet:
2.54 mm 90degrees, right angle male header

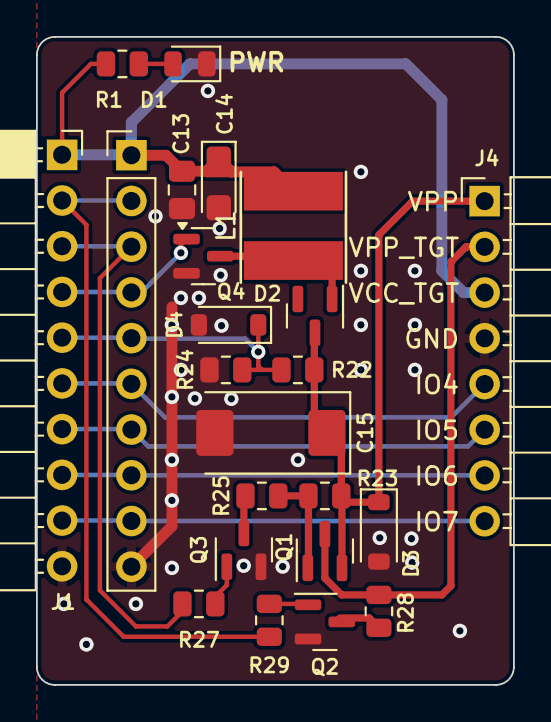
[picture p92: board vpp-maker-rev6-ian.kicad_pcb from above]

Board: 2 copper layers, 26.5 x 36.0 mm, 23 parts (0 on the bottom side), 19 nets.
