DangerousPrototypes/BusPirate5-hardware/adapter-rs232-dual-1REV0/rs232-dual-adapter.kicad_pcb

## KiCad design adapter-rs232-dual-1REV0/rs232-dual-adapter.kicad_pcb (2025-06-16)

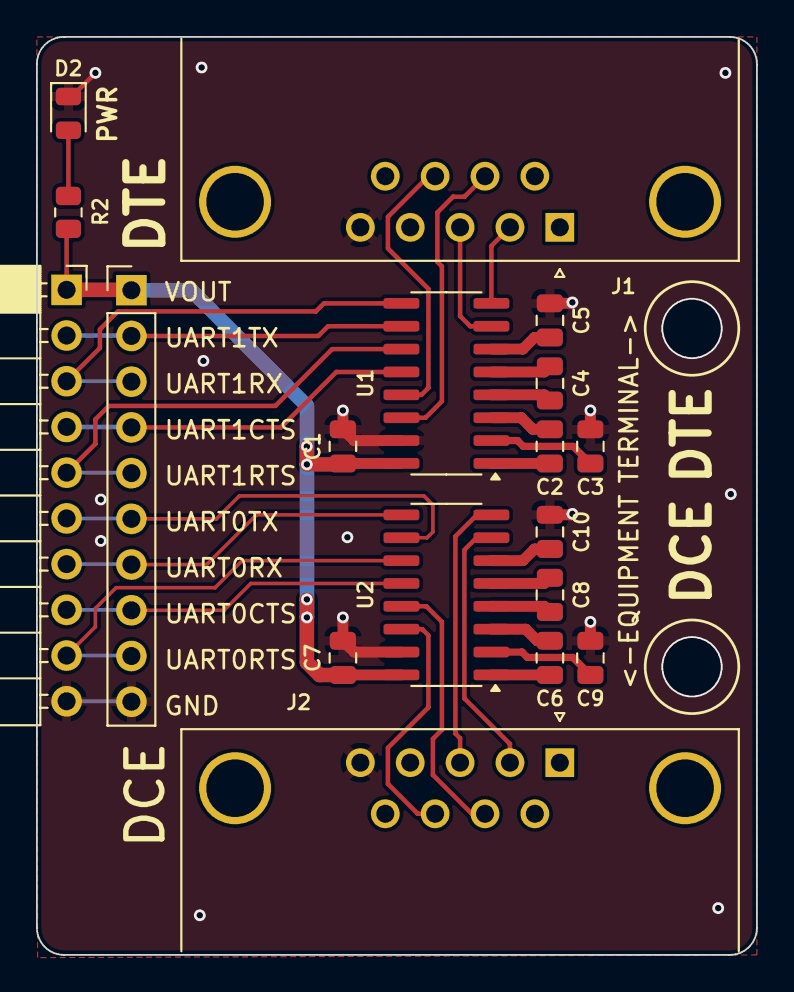
[picture p93: board rs232-dual-adapter.kicad_pcb from above]

Board: 2 copper layers, 40.0 x 51.0 mm, 18 parts (0 on the bottom side), 31 nets.

Parts:
C1, C2, C6, C7: 0.1uF; C_0805_2012Metric
C3, C4, C5, C8, C9, C10: 0.47uF; C_0805_2012Metric
D2: LED; LED_0805_2012Metric
J1: COM1; DSUB-9_Male_Horizontal_P2.77x2.84mm_EdgePinOffset7.70mm_Hou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
J2: COM2; DSUB-9_Female_Horizontal_P2.77x2.84mm_EdgePinOffset7.70mm_H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
J3: Conn_01x10; PinHeader_1x10_P2.54mm_Vertical
J4: Conn_01x10; PinSocket_1x10_P2.54mm_Horizontal
R2: 2K; R_0805_2012Metric
U1, U2: MAX3232; SOP-16_3.9x9.9mm_P1.27mm

Connections:
/DCE_CTS: J2.8, U2.14 (T1OUT)
/DCE_RTS: J2.7, U2.13 (R1IN)
/DCE_RXD: J2.2, U2.7 (T2OUT)
/DCE_TXD: J2.3, U2.8 (R2IN)
/DTE_CTS: J1.8, U1.13 (R1IN)
/DTE_RTS: J1.7, U1.14 (T1OUT)
/DTE_RXD: J1.2, U1.8 (R2IN)
/DTE_TXD: J1.3, U1.7 (T2OUT)
GND: C1.2, C3.2, C5.2, C7.2, C9.2, C10.2, D2.1 (K), J1.5, J2.5, J3.10, J4.10, U1.15 (GND), U2.15 (GND)
unnamed: D2.2 (A), R2.2
unnamed: C2.1, U1.1 (C1+)
unnamed: C2.2, U1.3 (C1-)
unnamed: C4.1, U1.4 (C2+)
unnamed: C4.2, U1.5 (C2-)
unnamed: C3.1, U1.2 (VS+)
unnamed: C5.1, U1.6 (VS-)
unnamed: C6.1, U2.1 (C1+)
unnamed: C6.2, U2.3 (C1-)
unnamed: C8.1, U2.4 (C2+)
unnamed: C8.2, U2.5 (C2-)
unnamed: C9.1, U2.2 (VS+)
unnamed: C10.1, U2.6 (VS-)
UART0CTS: J3.8, J4.8, U2.12 (R1OUT)
UART0RTS: J3.9, J4.9, U2.11 (T1IN)
UART0RX: J3.7, J4.7, U2.9 (R2OUT)
UART0TX: J3.6, J4.6, U2.10 (T2IN)
UART1CTS: J3.4, J4.4, U1.12 (R1OUT)
UART1RTS: J3.5, J4.5, U1.11 (T1IN)
UART1RX: J3.3, J4.3, U1.9 (R2OUT)
UART1TX: J3.2, J4.2, U1.10 (T2IN)
VOUT: C1.1, C7.1, J3.1, J4.1, R2.1, U1.16 (VCC), U2.16 (VCC)
