DangerousPrototypes/BusPirate5-hardware/debug-station/programming_pin_mount.v1.0.kicad_pcb

## KiCad design debug-station/programming_pin_mount.v1.0.kicad_pcb (2023-09-21)

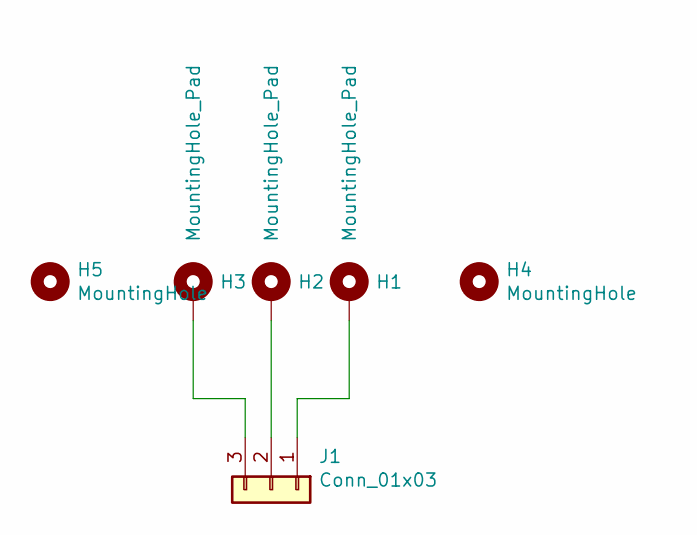
[picture p94: schematic programming_pin_mount.v1.0.sch]

Parts:
H1, H2, H3: MountingHole_Pad; PinHeader_1x01_P1.00mm_Vertical
H4, H5: MountingHole; MountingHole_3.2mm_M3
J1: Conn_01x03; PinHeader_1x03_P2.54mm_Horizontal

Connections:
unnamed: H1.1, J1.1
unnamed: H2.1, J1.2
unnamed: H3.1, J1.3

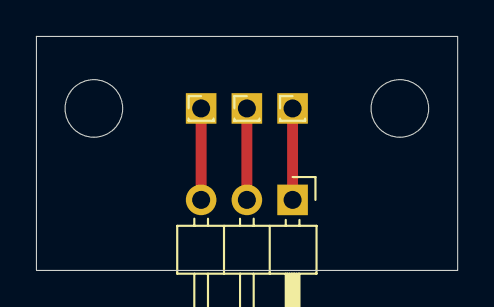
[picture p95: board programming_pin_mount.v1.0.kicad_pcb from above]

Board: 2 copper layers, 23.4 x 13.0 mm, 6 parts (0 on the bottom side), 3 nets.
